clutchfire3d/firestar/MarketingAssets/Firestar_Marketing_01.png

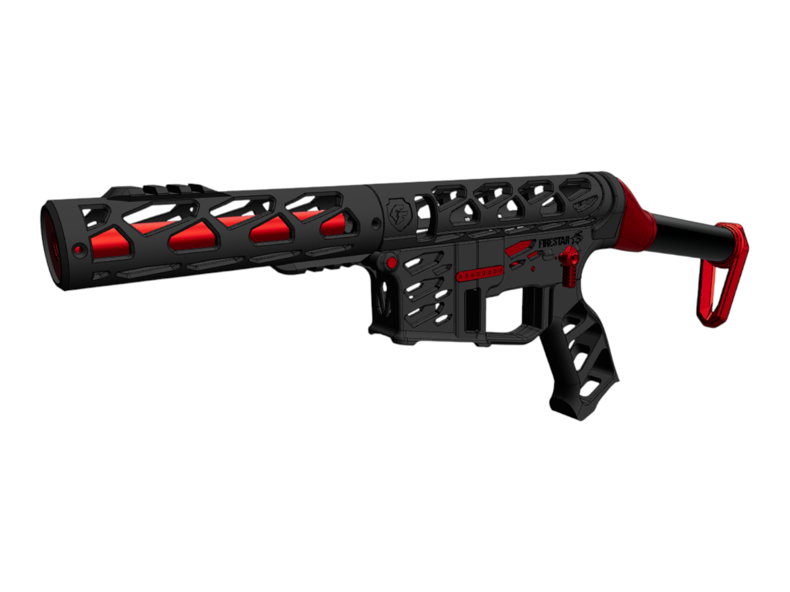
MarketingAssets/Firestar_Marketing_01.png
