clutchfire3d/firestar/MarketingAssets/Firestar_Marketing_02.png

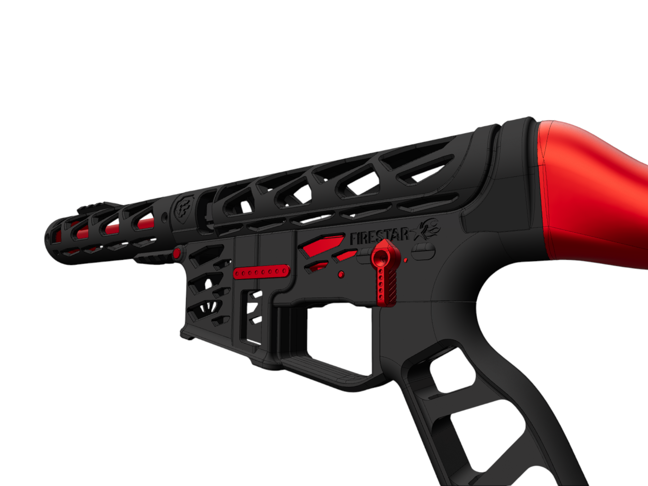
MarketingAssets/Firestar_Marketing_02.png
