clutchfire3d/firestar/MarketingAssets/Firestar_Marketing_03.png

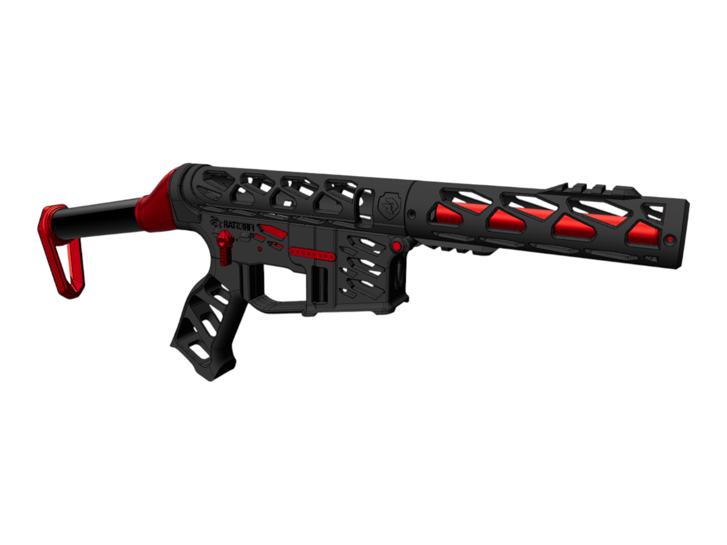
MarketingAssets/Firestar_Marketing_03.png
