clutchfire3d/firestar/MarketingAssets/Firestar_Marketing_04.png

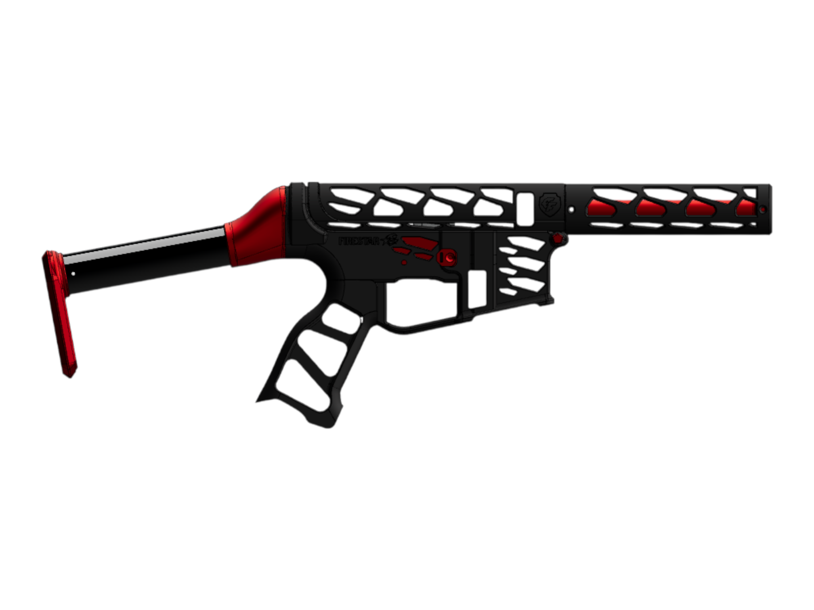
MarketingAssets/Firestar_Marketing_04.png
