clutchfire3d/firestar/MarketingAssets/Firestar_Marketing_05.png

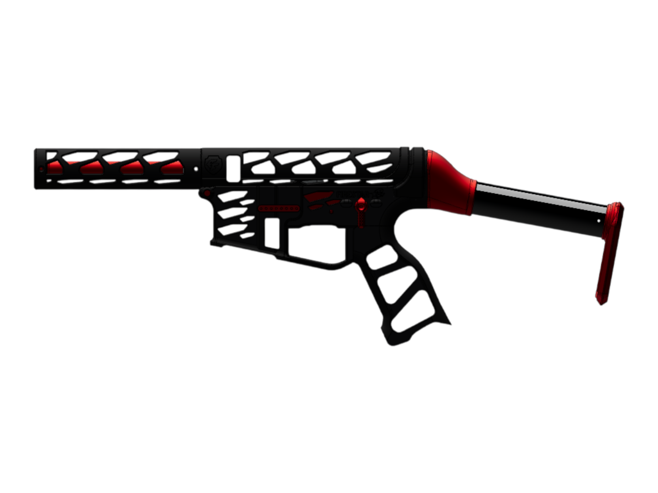
MarketingAssets/Firestar_Marketing_05.png
