clutchfire3d/firestar/MarketingAssets/Firestar_Marketing_06.png

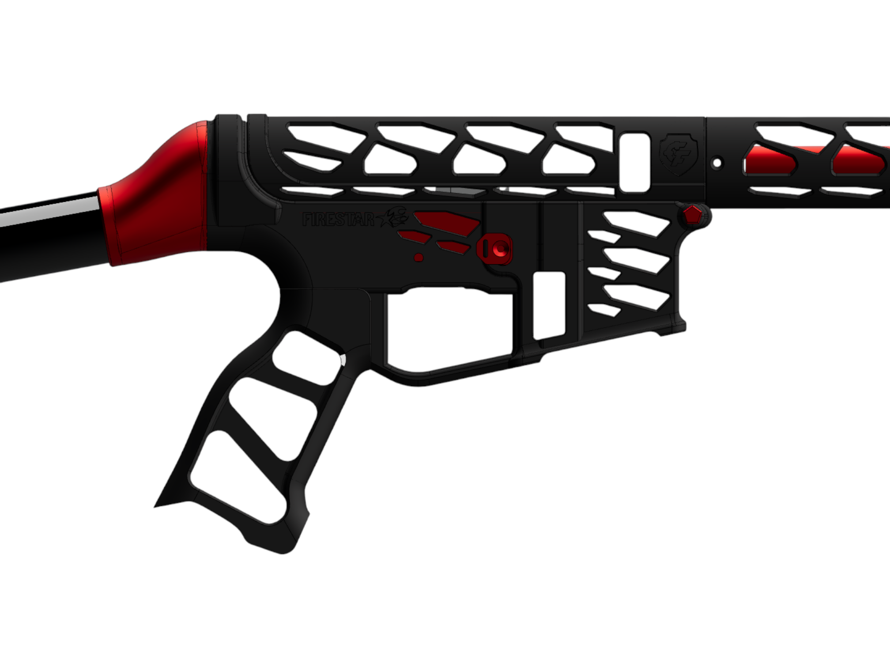
MarketingAssets/Firestar_Marketing_06.png
