clutchfire3d/firestar/Pages/Images/ClutchFireImg.jpg

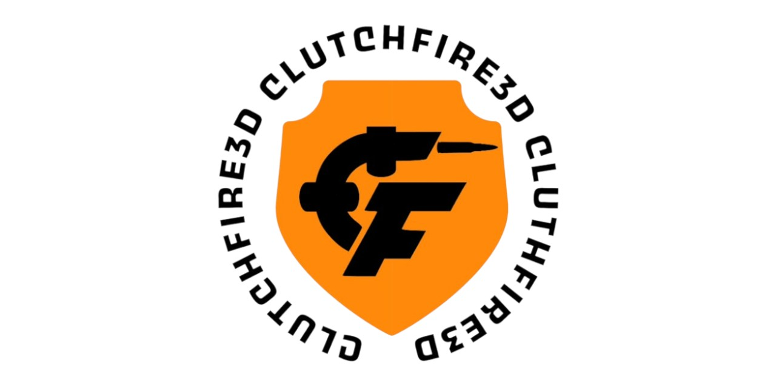
Pages/Images/ClutchFireImg.jpg
